JMW95/yuletronics/firmware/yuletronics_config.h

#ifndef YULETRONICS_CONFIG_H
#define YULETRONICS_CONFIG_H

// Whether to send/receive USB serial
#define USE_USB             FALSE

// Reduce brightness of LEDs to save power
#define LOW_BRIGHTNESS      TRUE

// Automatically advance animations, or require a button press
#define AUTO_ANIMATIONS     TRUE

// Whether the Flappy-bird easter egg is enabled
#define EASTER_EGG          TRUE

#endif /* YULETRONICS_CONFIG_H */
