JMW95/yuletronics/firmware/animations.h

#ifndef ANIMATIONS_H
#define ANIMATIONS_H

static const uint32_t ANIM_FIREWORK_PNG_DATA[] = {0x8000, 0x8000, 0x10000, 0x10000, 0x20000, 0x20000, 0x2000, 0x2000, 0x1000, 0x22880, 0x455544, 0xa8822a, 0x1100011};
static const uint32_t ANIM_SPINNER_PNG_DATA[] = {0x1041041, 0xc1060, 0x7c00, 0x19300, 0x111110, 0x211108, 0x421084, 0x841042, 0x1041041, 0xc1060, 0x7c00, 0x19300, 0x111110, 0x211108, 0x421084, 0x841042};

static const uint32_t *ANIMS[] = {
ANIM_FIREWORK_PNG_DATA, ANIM_SPINNER_PNG_DATA
};

static const uint32_t ANIM_LENS[] = {
13, 16
};

#define ANIM_FIREWORK_PNG 0
#define ANIM_SPINNER_PNG 1

#define NUM_ANIMS 2

#endif /* ANIMATIONS_H */
